mora200217/rus-med/ltspice/Ne_555_Buzzer.asc

C1: Cap; 0.0002µ
R1: Res; 10k
R2: Res; 1k
U1: NE555
V1: Voltage; 5
Named nets: 0, out
.tran 4m
