mora200217/rus-med/ltspice/Sim_PAI_PCB_01.asc

C2: Cap; 10µ
D1: zener
D4: Diode
M1: pmos
M2: pmos
R1: res; 1k
R2: Res; 100
U1: 78L05
V1: Voltage; SINE(0 20 1)
Named nets: 0, 1, 2, 3, 4
.tran 0 10 0 1
