mora200217/rus-med/ltspice/Draft1.asc

C1: Cap; 3.3m
C2: Cap; 3.3m
C3: Cap; 3.3m
C4: Cap; 200n
M1: nmos; Si7336ADP
Q2: npn; 2N2222
R1: Res; 450
R2: Res; 10k
R3: Res; 220k
R4: Res; 18k
R5: Res; 10
R6: Res; 2k
R7: Res; 20
V1: Voltage; 9
V2: Voltage; SINE(0 0.010 1k)
Named nets: 0, out, Vcc
.tran 3m
