mora200217/rus-med/ltspice/Draft2.asc

Q1: npn; 2N2222
R1: Res; 1k
V1: voltage; 5
V2: Voltage; {V}
Named nets: 0
.op
.step PARAM V 9 3 1
