mora200217/rus-med/ltspice/polarity_protec.asc

D1: zener; 1N750
M1: pmos; ZXM62P02E6
R1: Res; 1k
V1: Voltage; PULSE(-12 12 0 0.00001 0.00001 1 2 8)
Named nets: out, in, 0
.tran 8
Proteccion de polaridad
